Kekule-OXC/R3DUX/Research/smbus device addresses.png

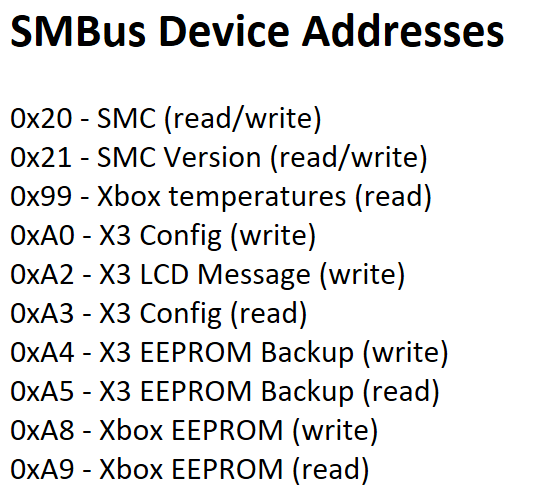
Research/smbus device addresses.png
