Kekule-OXC/R3DUX/Research/bank switch wiring diagram.jpg

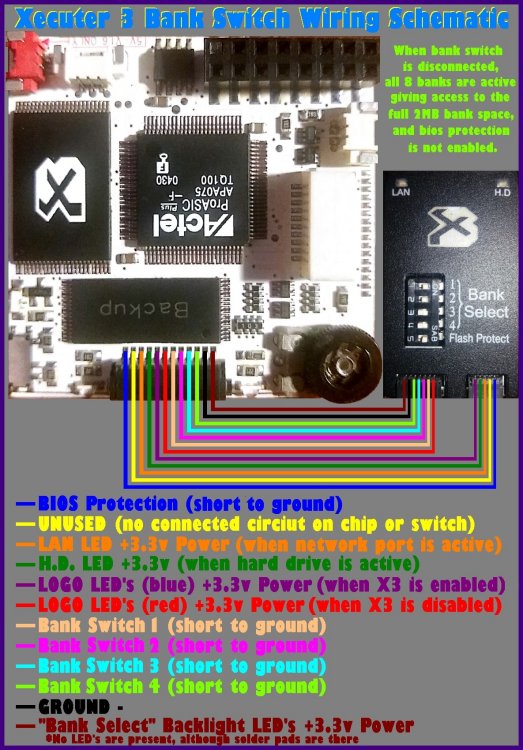
Research/bank switch wiring diagram.jpg
